eositis/a2-6502-analyzer/misc/a2-6502-signal-assignments.jpg

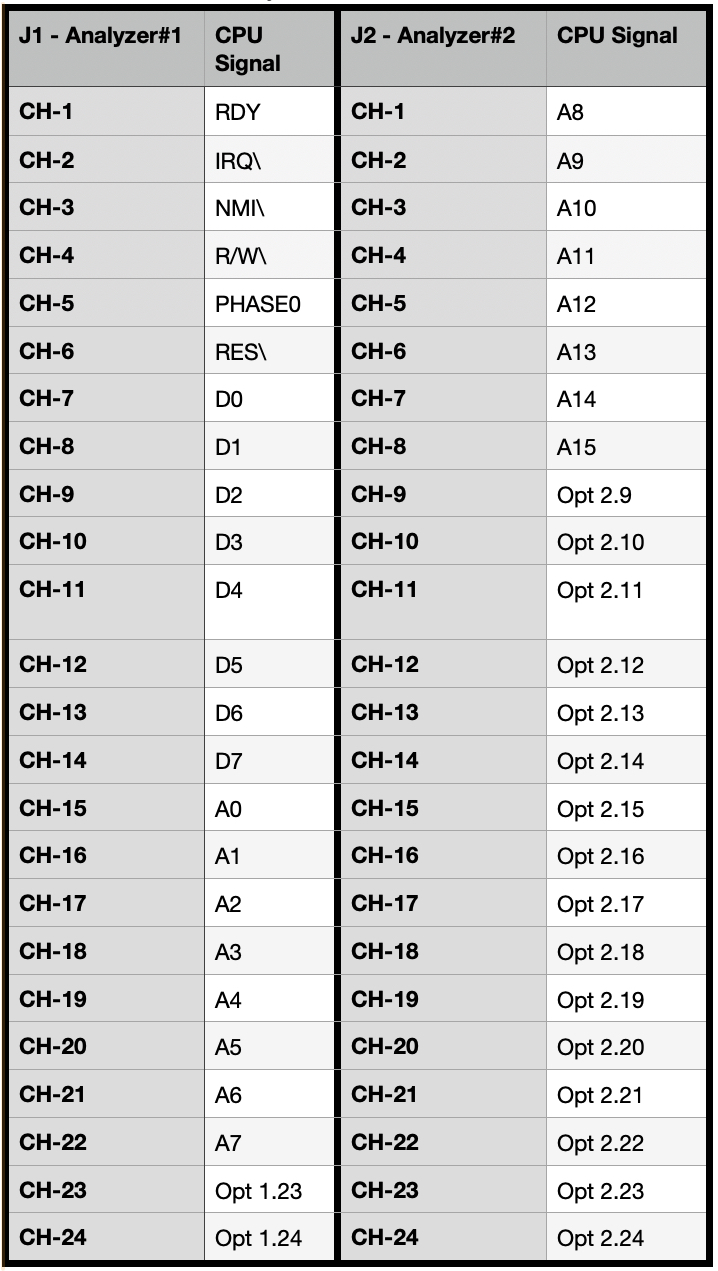
misc/a2-6502-signal-assignments.jpg
