eositis/a2-6502-analyzer/6502-interposer-ERRATA.gif

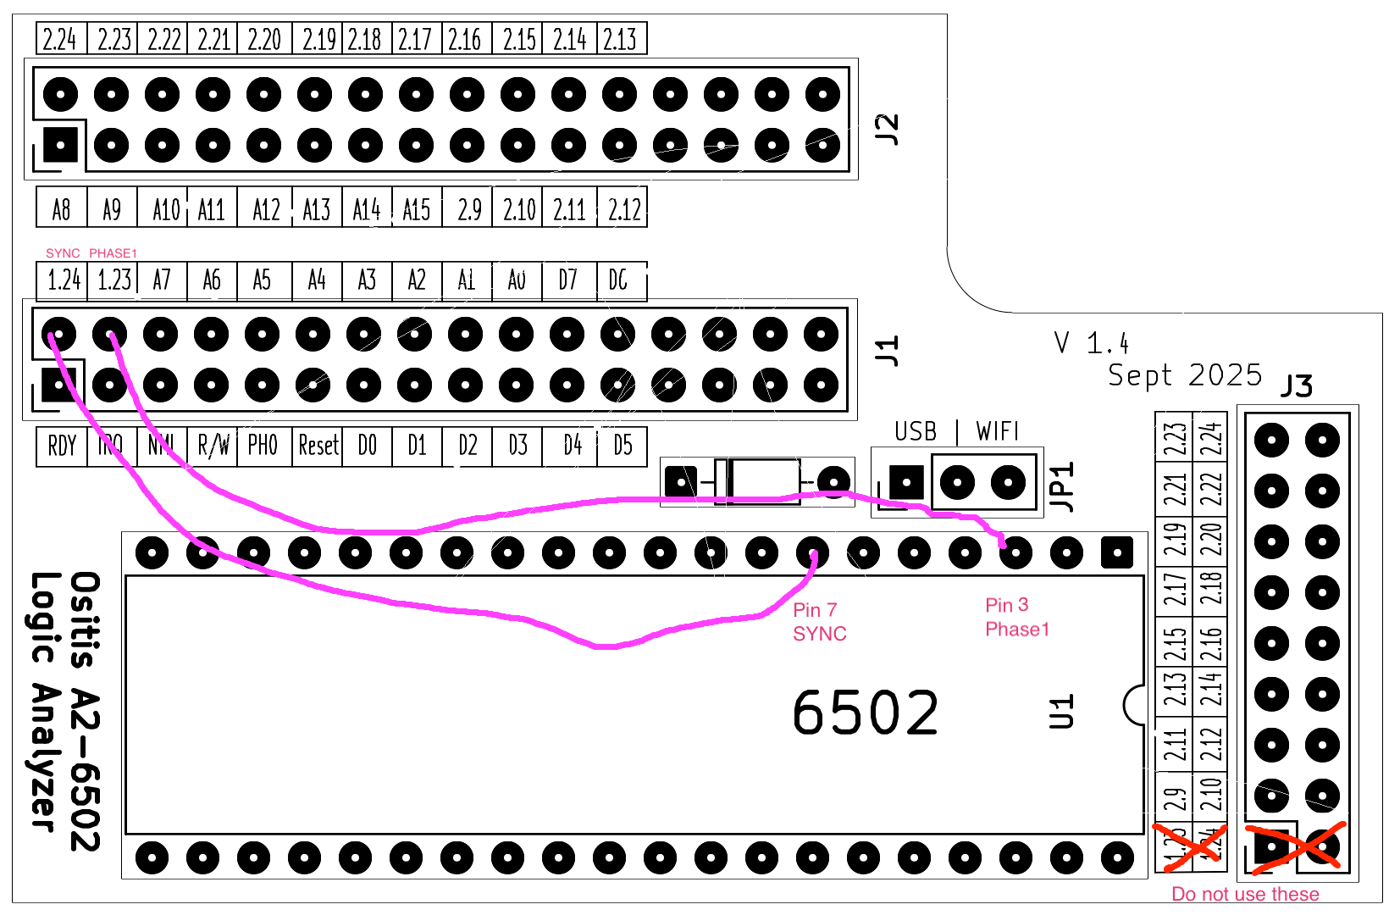
6502-interposer-ERRATA.gif
